TimotheeDvt/2026_NIME_TD/software/Source/DSP/Graph/GraphMappingStrategy.h

#pragma once

#include "../IMappingStrategy.h"
#include "../StaffMotionAnalyzer.h"
#include "NodeGraph.h"
#include <utility>
#include <vector>

namespace Graph {

// The one IMappingStrategy left once every preset is a NodeGraph - auto-registers a MonitorParam per sink port.
class GraphMappingStrategy : public IMappingStrategy {
public:
    GraphMappingStrategy(std::unique_ptr<NodeGraph> graph, juce::String displayName, juce::String description = {});

    const char* getName() const override { return name_.toRawUTF8(); }
    const juce::String& getDescription() const override { return description_; }
    void prepare(double sampleRate) override;
    bool process(const StaffSoundParams& in, MappingOutput& out) override;

    NodeGraph& getGraph() noexcept { return *graph_; }

private:
    juce::String name_;
    juce::String description_;
    StaffMotionAnalyzer motion_;
    std::unique_ptr<NodeGraph> graph_;
    // One entry per sink input port (a mega-sink node has many), not one per node.
    struct SinkMonitor { NodeId nodeId; int port; MonitorParam* param; };
    std::vector<SinkMonitor> sinkMonitors_;
};

} // namespace Graph
