TimotheeDvt/2026_NIME_TD/software/Source/DSP/Graph/Presets/AllPresets.h

#pragma once

#include "../NodeGraph.h"
#include <memory>

// One function per mapping strategy, each reproducing its behavior as a NodeGraph.
namespace Graph::Presets {

std::unique_ptr<NodeGraph> buildSimple();
std::unique_ptr<NodeGraph> buildWindNoise();
std::unique_ptr<NodeGraph> buildLeadDrone();
std::unique_ptr<NodeGraph> buildSpinFilter();
std::unique_ptr<NodeGraph> buildBowedChord();
std::unique_ptr<NodeGraph> buildAzimut();
std::unique_ptr<NodeGraph> buildAzimutPlus();
std::unique_ptr<NodeGraph> buildAzimutReverb();
std::unique_ptr<NodeGraph> buildAzimutKinetic();
std::unique_ptr<NodeGraph> buildMartialEffort();
std::unique_ptr<NodeGraph> buildMartialMomentum();
std::unique_ptr<NodeGraph> buildSpinVoice();
std::unique_ptr<NodeGraph> buildSpinVoiceScale();
std::unique_ptr<NodeGraph> buildSpeedGate();
std::unique_ptr<NodeGraph> buildVocalTract();

} // namespace Graph::Presets
