TimotheeDvt/2026_NIME_TD/software/Source/DSP/Graph/GraphTypes.h

#pragma once

#include "../StaffMotionAnalyzer.h"
#include <JuceHeader.h>
#include <array>
#include <cstdint>
#include <memory>

struct StaffSoundParams;
struct MappingOutput;

namespace Graph {

using NodeId = int32_t;
constexpr NodeId kInvalidNodeId = -1;

// Most node types need only a handful; the "Additive Synth" mega-sink needs one port per
// synth parameter (AdditivePort::Count), which sets the upper bound for both.
constexpr int kMaxNodeOutputs = 40;
constexpr int kMaxNodeInputs = 40;

// Unconnected falls back to defaultValue.
struct InputSlot {
    NodeId sourceNode = kInvalidNodeId;
    int sourceOutputPort = 0;
    float defaultValue = 0.0f;
};

// Stateless node types never allocate one.
struct NodeState {
    virtual ~NodeState() = default;
    virtual void prepare(double sampleRate) { juce::ignoreUnused(sampleRate); reset(); }
    virtual void reset() {}
};

// `analyzer` is a live, mutable reference since Spin Classification must call back into it directly.
struct SourceFrame {
    const StaffSoundParams& raw;
    const StaffMotionAnalyzer::DerivedMotionFrame& derived;
    StaffMotionAnalyzer& analyzer;
};

} // namespace Graph
