TimotheeDvt/2026_NIME_TD/software/Source/DSP/Graph/NodeTypeRegistry.cpp

#include "NodeMetadata.h"
#include "NodeTypeRegistry.h"

namespace Graph {

NodeTypeRegistry& NodeTypeRegistry::instance() {
    static NodeTypeRegistry registry;
    return registry;
}

NodeTypeRegistry::NodeTypeRegistry() {
    registerAllNodes(*this);
}

void NodeTypeRegistry::registerType(NodeTypeInfo info) {
    jassert(find(info.id) == nullptr && "duplicate node type id registered");
    indexById_[info.id.toStdString()] = types_.size();
    types_.push_back(std::move(info));
}

const NodeTypeInfo* NodeTypeRegistry::find(const juce::String& typeId) const {
    auto it = indexById_.find(typeId.toStdString());
    if (it == indexById_.end())
        return nullptr;
    return &types_[it->second];
}

} // namespace Graph
