TimotheeDvt/2026_NIME_TD/software/Source/UI/RawDataWindow.h

#pragma once

#include "../PluginProcessor.h"
#include <JuceHeader.h>

class RawDataComponent : public juce::Component, private juce::Timer {
public:
  explicit RawDataComponent(REMORAProcessor &);
  ~RawDataComponent() override;

  void paint(juce::Graphics &) override;
  void resized() override;
  void timerCallback() override;

private:
  REMORAProcessor &processor;

  juce::Label rateValueLabel;
  juce::Label rateUnitLabel;
  juce::Label totalLabel;
  juce::Label totalValueLabel;
  juce::Label ipLabel;
  juce::Label ipValueLabel;

  juce::Label accelHeaderLabel;
  juce::Label axLabel, ayLabel, azLabel;
  juce::Label axVal, ayVal, azVal;

  juce::Label gyroHeaderLabel;
  juce::Label gxLabel, gyLabel, gzLabel;
  juce::Label gxVal, gyVal, gzVal;

  juce::Label magHeaderLabel;
  juce::Label mxLabel, myLabel, mzLabel;
  juce::Label mxVal, myVal, mzVal;

  juce::Label eulerHeaderLabel;
  juce::Label pitchLabel, rollLabel, yawLabel;
  juce::Slider pitchSlider, rollSlider, yawSlider;

  static juce::String fmt(float v, int decimals = 3);
  static juce::Colour rateColour(float msgPerSec);

  JUCE_DECLARE_NON_COPYABLE_WITH_LEAK_DETECTOR(RawDataComponent)
};

class RawDataWindow : public juce::DocumentWindow {
public:
  explicit RawDataWindow(REMORAProcessor &p);
  void closeButtonPressed() override;

private:
  RawDataComponent content;
  JUCE_DECLARE_NON_COPYABLE_WITH_LEAK_DETECTOR(RawDataWindow)
};
